LikeFall123/Impedance_Measurement/Simulations/DAC_Filter.asc

B2: bv; V={floor(V(vs0)/vrange*nlevels)/nlevels*vrange}
C1: cap; 1n
C2: cap; 500p
R1: res; 3.3k
R2: res; 1.6k
R3: res; 3.3k
U2: UniversalOpAmp
V1: voltage; SINE(0 1 {f0})
V2: voltage; 5
V3: voltage; -5
Named nets: 0, DAC_Out, DAC_Out_Filtered, +5V, -5V, vs0
.tran 0 500u 0 5p
.param f0=1k fs=20k
.param vrange = 1
.param nlevels=65536
